AbhinavK02/LoRaProject/B.1 Schematic/LoRa_ESP32.png

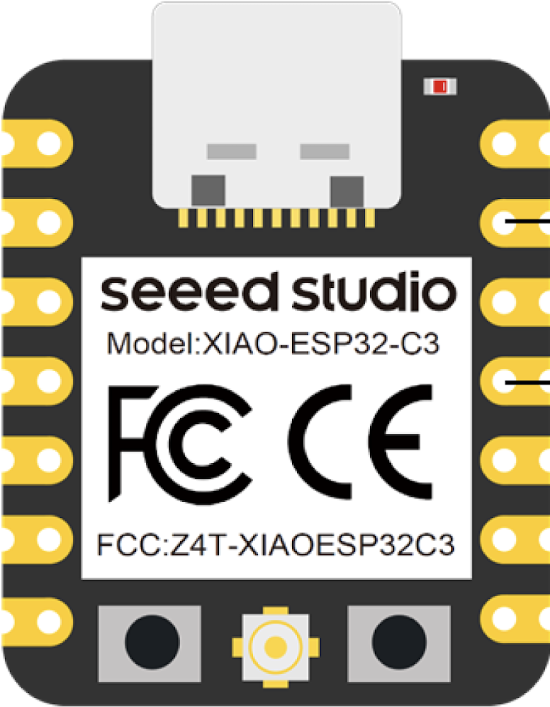
B.1 Schematic/LoRa_ESP32.png
