AbhinavK02/LoRaProject/B.1 Schematic/LoRA_Sch_V1.png

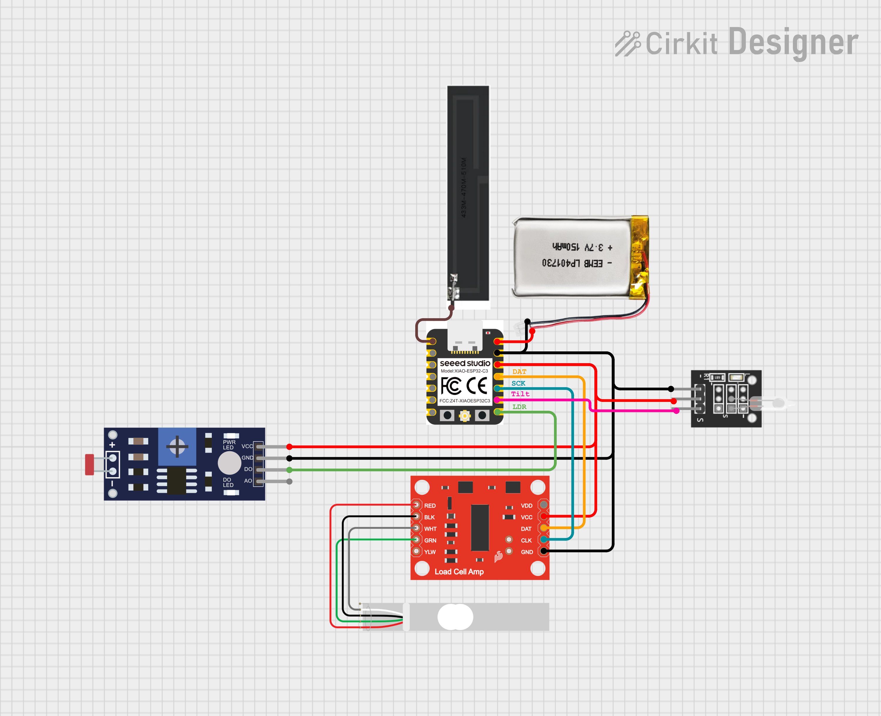
B.1 Schematic/LoRA_Sch_V1.png
