AbhinavK02/LoRaProject/B.1 Schematic/LoRa_Sch_V2.png

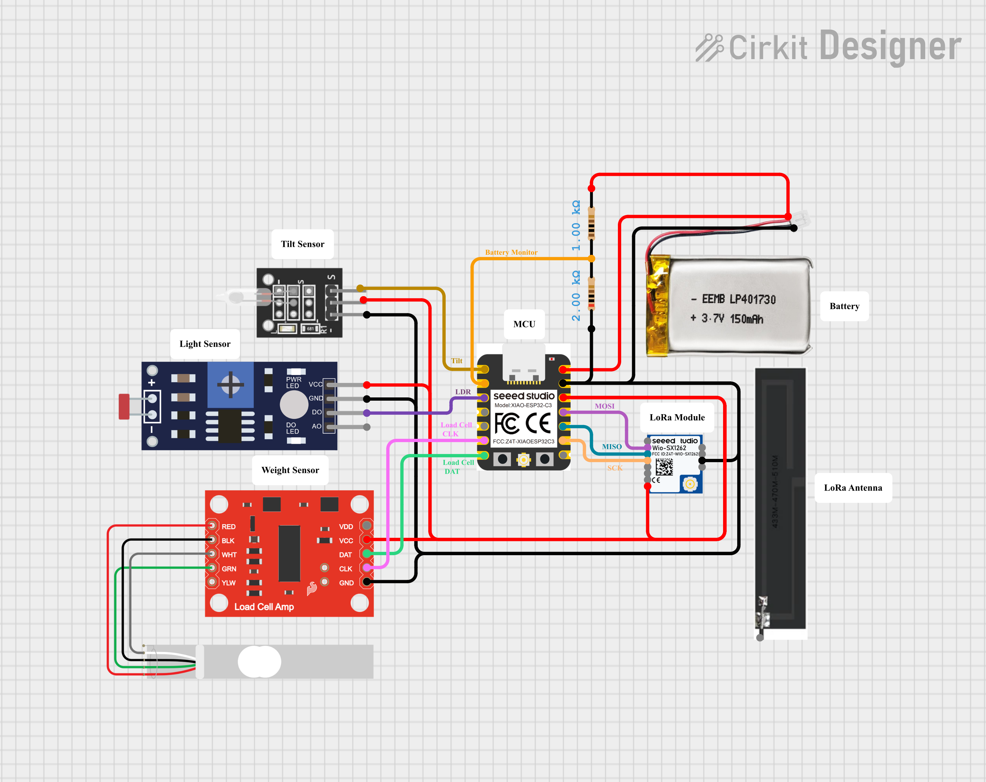
B.1 Schematic/LoRa_Sch_V2.png
