AbhinavK02/LoRaProject/C.1 Project Report and Presentation/assets/amazon-fouvin.jpg

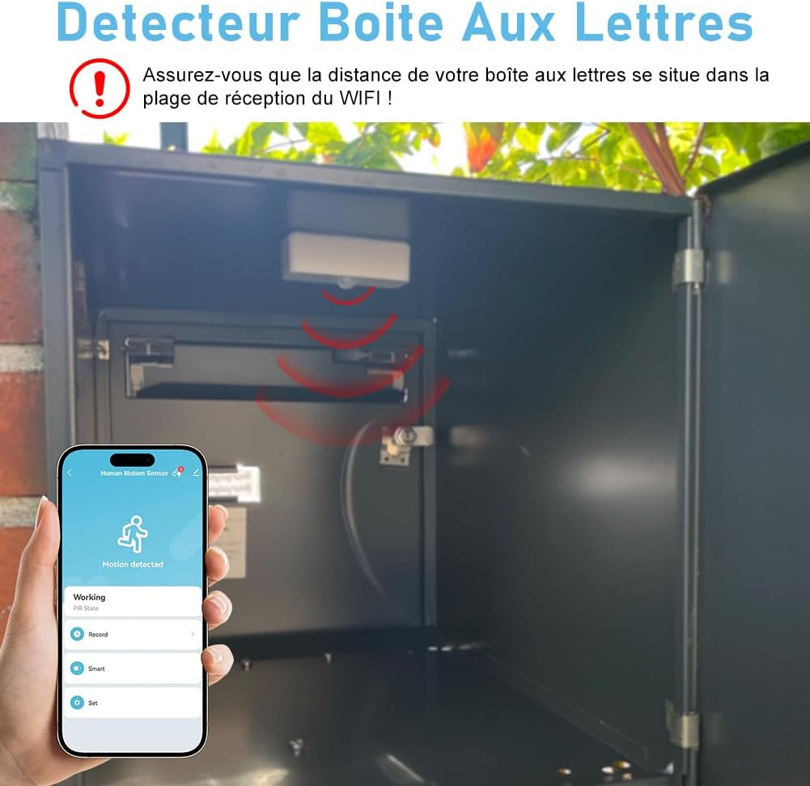
C.1 Project Report and Presentation/assets/amazon-fouvin.jpg
