AbhinavK02/LoRaProject/C.1 Project Report and Presentation/assets/datacake-dashboard.PNG

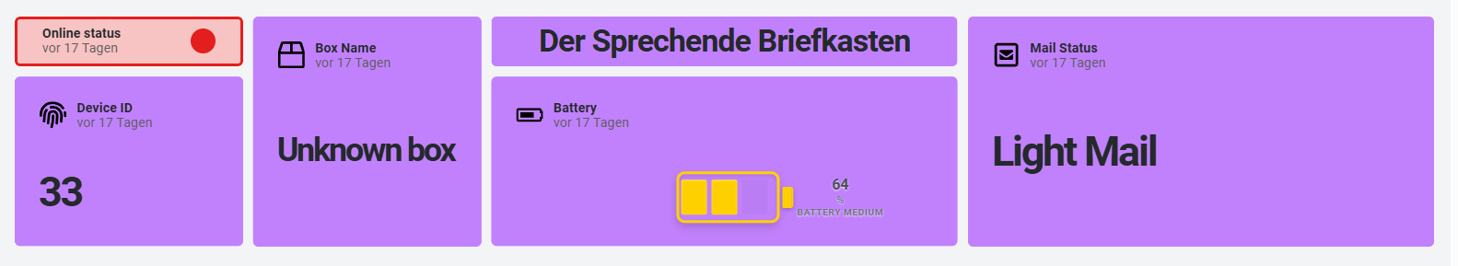
C.1 Project Report and Presentation/assets/datacake-dashboard.PNG
