AbhinavK02/LoRaProject/C.1 Project Report and Presentation/assets/finalProduct_underneath.jpg

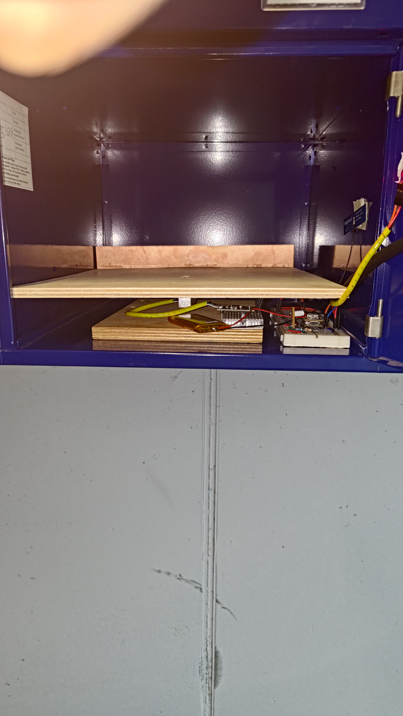
C.1 Project Report and Presentation/assets/finalProduct_underneath.jpg
