AbhinavK02/LoRaProject/C.1 Project Report and Presentation/assets/instaview.jpg

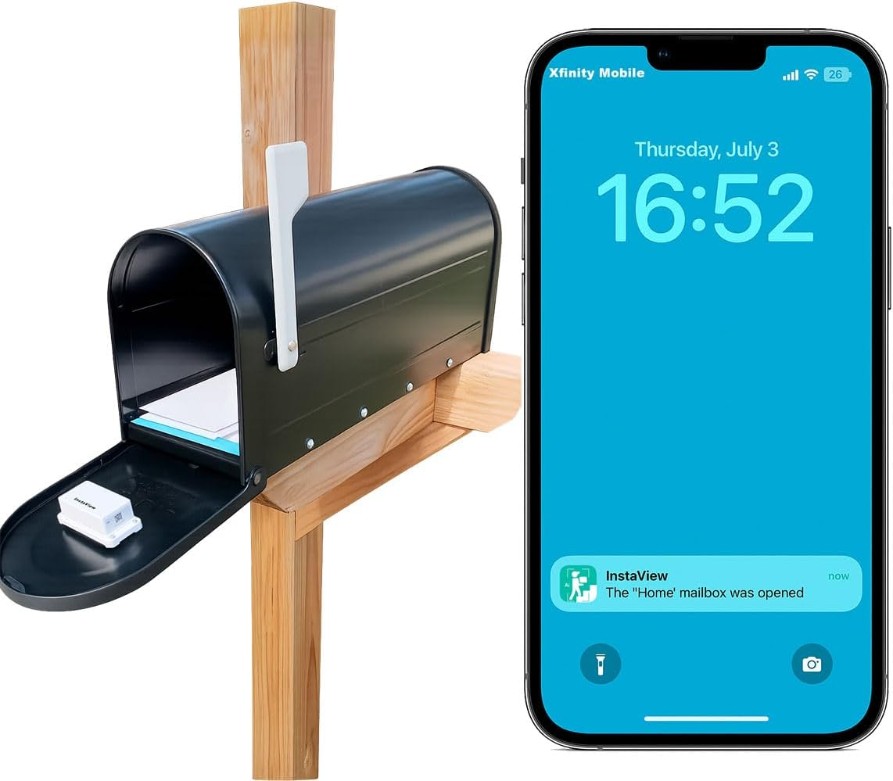
C.1 Project Report and Presentation/assets/instaview.jpg
