AbhinavK02/LoRaProject/C.1 Project Report and Presentation/assets/LoRa_FSD_Prez.png

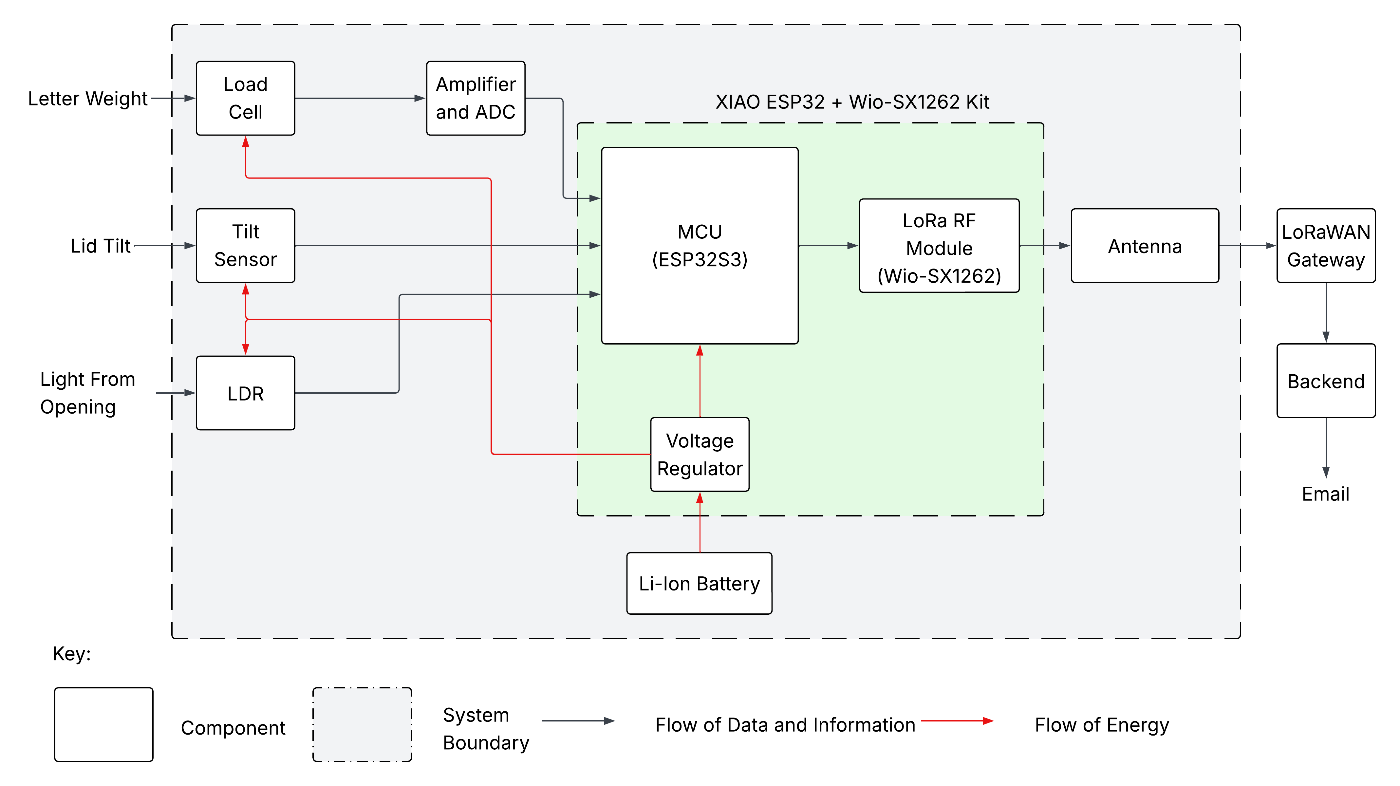
C.1 Project Report and Presentation/assets/LoRa_FSD_Prez.png
