AbhinavK02/LoRaProject/C.1 Project Report and Presentation/assets/system-flowchart_hor_short_transparent.png

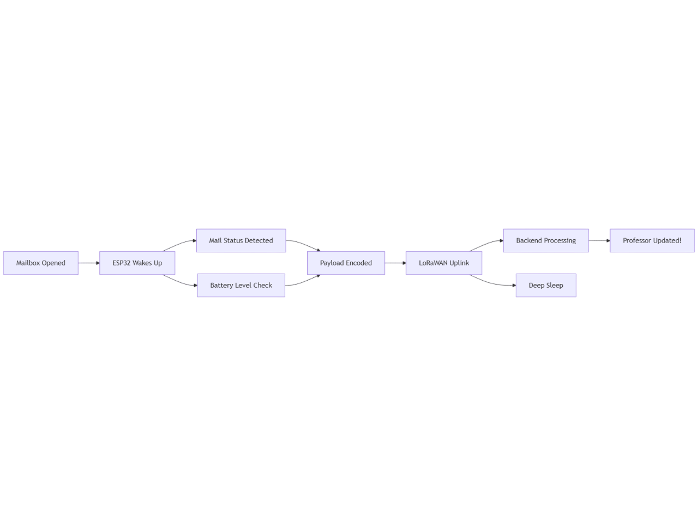
C.1 Project Report and Presentation/assets/system-flowchart_hor_short_transparent.png
