AbhinavK02/LoRaProject/C.1 Project Report and Presentation/assets/x-sense.jpg

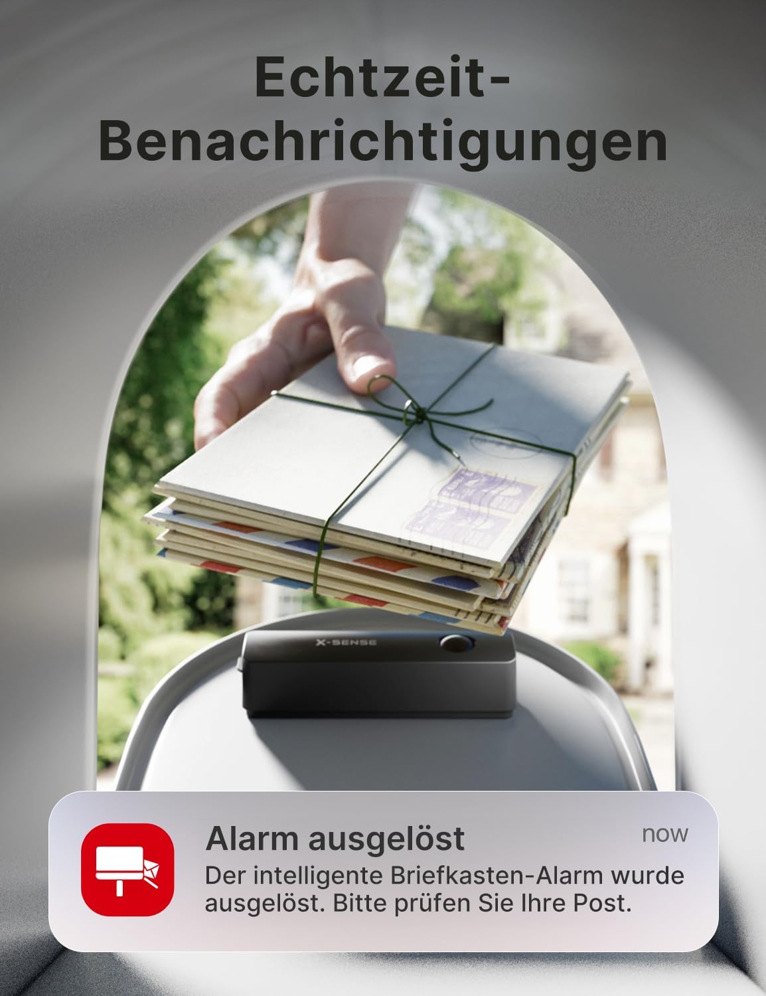
C.1 Project Report and Presentation/assets/x-sense.jpg
