AbhinavK02/LoRaProject/B.0 System Design/TheTalkingMailbox/TheTalkingMailbox.kicad_pcb

## KiCad design src/kicad/keyboard/8x8.kicad_sch


Parts:
D1, D2, D3, D4, D5, D6, D7, D8, D9, D10, D11, D12, D13, D14, D15, D16, D17, D18, D19, D20, D21, D22, D23, D24, D25, D26, D27, D28, D29, D30, D31, D32, D33, D34, D35, D36, D37, D39, D40, D41, D42, D43, D44, D45, D46, D47, D48, D49, D50, D51, D52, D53, D54, D55, D56, D57, D58, D59, D60: D
KEY_1, KEY_2, KEY_3, KEY_4, KEY_5, KEY_6, KEY_7, KEY_8, KEY_9, KEY_10: SW_Push
KEY_A1: SW_Push
KEY_ALT1: SW_Push
KEY_B1: SW_Push
KEY_BACK1: SW_Push
KEY_C1: SW_Push
KEY_COMMA1: SW_Push
KEY_CTRL1: SW_Push
KEY_D1: SW_Push
KEY_DOWN1: SW_Push
KEY_E1: SW_Push
KEY_EQUALS1: SW_Push
KEY_ESC1: SW_Push
KEY_F1: SW_Push
KEY_FN1: SW_Push
KEY_G1: SW_Push
KEY_H1: SW_Push
KEY_I1: SW_Push
KEY_J1: SW_Push
KEY_K1: SW_Push
KEY_L1: SW_Push
KEY_LEFT1: SW_Push
KEY_M1: SW_Push
KEY_MINUS1: SW_Push
KEY_N1: SW_Push
KEY_O1: SW_Push
KEY_OS1: SW_Push
KEY_P1: SW_Push
KEY_PERIOD1: SW_Push
KEY_Q1: SW_Push
KEY_QUOTE1: SW_Push
KEY_R1: SW_Push
KEY_RET1, KEY_RET2: SW_Push
KEY_RIGHT1: SW_Push
KEY_S1: SW_Push
KEY_SC1: SW_Push
KEY_SHIFT1: SW_Push
KEY_SLASH1: SW_Push
KEY_SPACE1, KEY_SPACE2: SW_Push
KEY_T1: SW_Push
KEY_TAB1: SW_Push
KEY_U1: SW_Push
KEY_UP1: SW_Push
KEY_V1: SW_Push
KEY_W1: SW_Push
KEY_X1: SW_Push
KEY_Y1: SW_Push
KEY_Z1: SW_Push
Pull-Up1, Pull-Up2, Pull-Up3, Pull-Up4, Pull-Up5, Pull-Up6, Pull-Up7, Pull-Up8: 1K

Connections:
+3.3V: Pull-Up1.1, Pull-Up2.1, Pull-Up3.1, Pull-Up4.1, Pull-Up5.1, Pull-Up6.1, Pull-Up7.1, Pull-Up8.1
GNDREF: D1.1 (K), D2.1 (K), D3.1 (K), D4.1 (K), D5.1 (K), D6.1 (K), D7.1 (K), D8.1 (K), D9.1 (K), D10.1 (K), D11.1 (K), D12.1 (K), D13.1 (K), D14.1 (K), D15.1 (K), D16.1 (K), D17.1 (K), D18.1 (K), D19.1 (K), D20.1 (K), D21.1 (K), D22.1 (K), D23.1 (K), D24.1 (K), D25.1 (K), D26.1 (K), D27.1 (K), D28.1 (K), D29.1 (K), D30.1 (K), D31.1 (K), D32.1 (K), D33.1 (K), D34.1 (K), D35.1 (K), D36.1 (K), D37.1 (K), D39.1 (K), D40.1 (K), D41.1 (K), D42.1 (K), D43.1 (K), D44.1 (K), D45.1 (K), D46.1 (K), D47.1 (K), D48.1 (K), D49.1 (K), D50.1 (K), D51.1 (K), D52.1 (K), D53.1 (K), D54.1 (K), D55.1 (K), D56.1 (K), D57.1 (K), D58.1 (K), D59.1 (K), D60.1 (K)
Input 1: KEY_1.1, KEY_2.1, KEY_4.1, KEY_5.1, KEY_6.1, KEY_7.1, KEY_8.1, KEY_10.1, Pull-Up1.2
Input 2: KEY_E1.1, KEY_Q1.1, KEY_R1.1, KEY_T1.1, KEY_TAB1.1, KEY_U1.1, KEY_W1.1, KEY_Y1.1, Pull-Up2.2
Input 3: KEY_A1.1, KEY_D1.1, KEY_ESC1.1, KEY_F1.1, KEY_G1.1, KEY_H1.1, KEY_J1.1, KEY_S1.1, Pull-Up3.2
Input 4: KEY_B1.1, KEY_C1.1, KEY_M1.1, KEY_N1.1, KEY_SHIFT1.1, KEY_V1.1, KEY_X1.1, KEY_Z1.1, Pull-Up4.2
Input 5: KEY_ALT1.1, KEY_CTRL1.1, KEY_OS1.1, KEY_RET1.1, KEY_RET2.1, KEY_SPACE1.1, KEY_SPACE2.1, Pull-Up5.2
Input 6: KEY_3.1, KEY_9.1, KEY_COMMA1.1, KEY_EQUALS1.1, KEY_MINUS1.1, KEY_PERIOD1.1, KEY_SLASH1.1, KEY_UP1.1, Pull-Up6.2
Input 7: KEY_BACK1.1, KEY_DOWN1.1, KEY_FN1.1, KEY_I1.1, KEY_LEFT1.1, KEY_O1.1, KEY_P1.1, KEY_RIGHT1.1, Pull-Up7.2
Input 8: KEY_K1.1, KEY_L1.1, KEY_QUOTE1.1, KEY_SC1.1, Pull-Up8.2
unnamed: D1.2 (A), KEY_1.2
unnamed: D2.2 (A), KEY_2.2
unnamed: D3.2 (A), KEY_4.2
unnamed: D4.2 (A), KEY_5.2
unnamed: D5.2 (A), KEY_6.2
unnamed: D6.2 (A), KEY_7.2
unnamed: D7.2 (A), KEY_8.2
unnamed: D8.2 (A), KEY_10.2
unnamed: D9.2 (A), KEY_TAB1.2
unnamed: D10.2 (A), KEY_Q1.2
unnamed: D11.2 (A), KEY_W1.2
unnamed: D12.2 (A), KEY_E1.2
unnamed: D13.2 (A), KEY_R1.2
unnamed: D14.2 (A), KEY_T1.2
unnamed: D15.2 (A), KEY_Y1.2
unnamed: D16.2 (A), KEY_U1.2
unnamed: D17.2 (A), KEY_ESC1.2
unnamed: D18.2 (A), KEY_A1.2
unnamed: D19.2 (A), KEY_S1.2
unnamed: D20.2 (A), KEY_D1.2
unnamed: D21.2 (A), KEY_F1.2
unnamed: D22.2 (A), KEY_G1.2
unnamed: D23.2 (A), KEY_H1.2
unnamed: D24.2 (A), KEY_J1.2
unnamed: D25.2 (A), KEY_SHIFT1.2
unnamed: D26.2 (A), KEY_Z1.2
unnamed: D27.2 (A), KEY_X1.2
unnamed: D28.2 (A), KEY_C1.2
unnamed: D29.2 (A), KEY_V1.2
unnamed: D30.2 (A), KEY_B1.2
unnamed: D31.2 (A), KEY_N1.2
unnamed: D32.2 (A), KEY_M1.2
unnamed: D33.2 (A), KEY_CTRL1.2
unnamed: D34.2 (A), KEY_OS1.2
unnamed: D35.2 (A), KEY_ALT1.2
unnamed: D36.2 (A), KEY_SPACE1.2
unnamed: D37.2 (A), KEY_SPACE2.2
unnamed: D39.2 (A), KEY_RET1.2
unnamed: D40.2 (A), KEY_RET2.2
unnamed: D41.2 (A), KEY_9.2
unnamed: D42.2 (A), KEY_3.2
unnamed: D43.2 (A), KEY_MINUS1.2
unnamed: D44.2 (A), KEY_EQUALS1.2
unnamed: D45.2 (A), KEY_COMMA1.2
unnamed: D46.2 (A), KEY_PERIOD1.2
unnamed: D47.2 (A), KEY_UP1.2
unnamed: D48.2 (A), KEY_SLASH1.2
unnamed: D49.2 (A), KEY_I1.2
unnamed: D50.2 (A), KEY_O1.2
unnamed: D51.2 (A), KEY_P1.2
unnamed: D52.2 (A), KEY_BACK1.2
unnamed: D53.2 (A), KEY_FN1.2
unnamed: D54.2 (A), KEY_LEFT1.2
unnamed: D55.2 (A), KEY_DOWN1.2
unnamed: D56.2 (A), KEY_RIGHT1.2
unnamed: D57.2 (A), KEY_K1.2
unnamed: D58.2 (A), KEY_L1.2
unnamed: D59.2 (A), KEY_SC1.2
unnamed: D60.2 (A), KEY_QUOTE1.2

Notes on the sheet:
Inputs, Pull-up high
Outputs (Low)
