AbhinavK02/LoRaProject/B.4 Code/Testing-LoRa/HX711_calibration/HX711_calibration.ino

/**
 *
 * HX711 library for Arduino - example file
 * https://github.com/bogde/HX711
 *
 * MIT License
 * (c) 2018 Bogdan Necula
 *
**/
#include "HX711.h"


// HX711 circuit wiring
const int LOADCELL_DOUT_PIN = 43;
const int LOADCELL_SCK_PIN = 6;


HX711 scale;

void setup() {
  Serial.begin(38400);
  Serial.println("HX711 Demo");

  Serial.println("Initializing the scale");

  // Initialize library with data output pin, clock input pin and gain factor.
  // Channel selection is made by passing the appropriate gain:
  // - With a gain factor of 64 or 128, channel A is selected
  // - With a gain factor of 32, channel B is selected
  // By omitting the gain factor parameter, the library
  // default "128" (Channel A) is used here.
  scale.begin(LOADCELL_DOUT_PIN, LOADCELL_SCK_PIN);
  scale.set_scale();
  scale.tare();
  Serial.println("Before setting up the scale:");
  Serial.print("read: \t\t");
  Serial.println(scale.read());			// print a raw reading from the ADC

  Serial.print("read average: \t\t");
  Serial.println(scale.read_average(20));  	// print the average of 20 readings from the ADC

  Serial.print("get value: \t\t");
  Serial.println(scale.get_value(10));		// print the average of 5 readings from the ADC minus the tare weight (not set yet)

  Serial.print("get units: \t\t");
  Serial.println(scale.get_units(10), 1);	// print the average of 5 readings from the ADC minus tare weight (not set) divided

  scale.set_scale(955.f); // Set the default 
  scale.tare();

  Serial.println("Readings:");
}

void loop() {
  Serial.print("one reading:\t");
  Serial.println(scale.get_units(10), 1);
  // Serial.print("\t| average:\t");
  // Serial.println(scale.get_units(10), 1);

  // scale.power_down();			        // put the ADC in sleep mode
  delay(5000);
  // scale.power_up();
}
